DAVe3283/MIDI-Chimes/Firmware/Teensy3.1/Master/bsod_win10.cpp

#include "bsod_win10.h"
#include <stdint.h>

// const uint16_t bsod_bg_windows_xp(0x0010); // #000082 --> RGB565
// const uint16_t bsod_fg_windows_xp(0xFFFF); // #FFFFFF --> RGB565
const uint16_t bsod_bg_windows_10(0x2336); // #2067B2 --> RGB565
const uint16_t bsod_fg_windows_10(0xFFFF); // #FFFFFF --> RGB565

// Run-length encoded. Byte 0 is run length, 1-2 are color (little-endian).
const size_t bsod_frown_width(44);
const size_t bsod_frown_height(84); // Encoded height is only 42, but we mirror it
const uint8_t bsod_frown[] =
{
    0x24, 0x36, 0x23, 0x01, 0x56, 0x23, 0x06, 0x78, 0x54, 0x01, 0x38, 0x4C,
    0x24, 0x36, 0x23, 0x01, 0x1C, 0xA6, 0x06, 0xFF, 0xFF, 0x01, 0xD9, 0x6C,
    0x23, 0x36, 0x23, 0x01, 0x1A, 0x75, 0x06, 0xFF, 0xFF, 0x01, 0x1B, 0xA6,
    0x23, 0x36, 0x23, 0x01, 0x38, 0x4C, 0x01, 0xDF, 0xFF, 0x05, 0xFF, 0xFF,
    0x01, 0x1E, 0xD7, 0x01, 0x56, 0x23, 0x22, 0x36, 0x23, 0x01, 0x97, 0x33,
    0x01, 0x7E, 0xE7, 0x05, 0xFF, 0xFF, 0x01, 0xBF, 0xF7, 0x01, 0xF7, 0x3B,
    0x23, 0x36, 0x23, 0x01, 0x9D, 0xBE, 0x06, 0xFF, 0xFF, 0x01, 0x19, 0x75,
    0x23, 0x36, 0x23, 0x01, 0xD9, 0x6C, 0x06, 0xFF, 0xFF, 0x01, 0x9D, 0xBE,
    0x23, 0x36, 0x23, 0x01, 0x96, 0x2B, 0x01, 0x7E, 0xE7, 0x05, 0xFF, 0xFF,
    0x01, 0xBF, 0xF7, 0x01, 0xD7, 0x3B, 0x23, 0x36, 0x23, 0x01, 0xFB, 0xA5,
    0x06, 0xFF, 0xFF, 0x01, 0x5A, 0x85, 0x23, 0x36, 0x23, 0x01, 0x58, 0x54,
    0x06, 0xFF, 0xFF, 0x01, 0xFD, 0xCE, 0x01, 0x56, 0x23, 0x23, 0x36, 0x23,
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
    0x01, 0x9E, 0xEF, 0x02, 0x36, 0x23, 0x01, 0x56, 0x23, 0x01, 0x5E, 0xDF,
    0x01, 0x3E, 0xDF, 0x01, 0xF7, 0x3B, 0x3C, 0x36, 0x23, 0x02, 0xDD, 0xC6,
    0x3F, 0x36, 0x23, 0x02, 0xDD, 0xC6, 0x09, 0x36, 0x23, 0x01, 0x5E, 0xE7,
    0x01, 0x3C, 0xAE, 0x1B, 0x36, 0x23, 0x01, 0x96, 0x2B, 0x01, 0xBF, 0xF7,
    0x01, 0x7C, 0xBE, 0x02, 0x36, 0x23, 0x01, 0x38, 0x4C, 0x01, 0xFF, 0xFF,
    0x01, 0x19, 0x75, 0x04, 0x36, 0x23, 0x01, 0x56, 0x23, 0x01, 0x98, 0x5C,
    0x02, 0x3A, 0x7D, 0x01, 0x58, 0x54, 0x04, 0x36, 0x23, 0x01, 0xF7, 0x3B,
    0x01, 0x19, 0x75, 0x04, 0x36, 0x23, 0x01, 0x76, 0x2B, 0x01, 0x19, 0x75,
    0x01, 0xF7, 0x3B, 0x02, 0x36, 0x23, 0x01, 0x58, 0x54, 0x01, 0xD9, 0x6C,
    0x01, 0x36, 0x23, 0x01, 0xF7, 0x3B, 0x01, 0x19, 0x75, 0x01, 0xB7, 0x33,
    0x06, 0x36, 0x23, 0x01, 0x5E, 0xE7, 0x01, 0x3C, 0xAE, 0x04, 0x36, 0x23,
    0x01, 0xBB, 0x95, 0x01, 0xFF, 0xFF, 0x01, 0xB7, 0x33, 0x01, 0x36, 0x23,
    0x01, 0xBB, 0x95, 0x01, 0xFF, 0xFF, 0x01, 0x58, 0x54, 0x0E, 0x36, 0x23,
    0x01, 0x19, 0x75, 0x01, 0x18, 0x4C, 0x01, 0x36, 0x23, 0x01, 0x58, 0x54,
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
};

void draw_BSOD(ILI9341_t3& display)
{
    // Set colors
    display.fillScreen(bsod_bg_windows_10);
    display.setTextColor(bsod_fg_windows_10);

    // Decompression buffer (holds one row)
    uint16_t buffer[max(bsod_frown_width, bsod_text_width)];

    // Decompress :( emoticon
    size_t x(0);
    int16_t y(0);
    for (size_t i(0); i < (sizeof(bsod_frown) / sizeof(bsod_frown[0])); i += 3)
    {
        size_t run_length(bsod_frown[i]);
        const uint16_t color(*reinterpret_cast<const uint16_t*>(bsod_frown + i + 1));
        for (size_t run(0); run < run_length; ++run)
        {
            buffer[x++] = color;
            if (x >= bsod_frown_width)
            {
                // Draw the buffer
                display.writeRect(20, 20 + y++, bsod_frown_width, 1, buffer);
                display.writeRect(20, 20 + bsod_frown_height - y, bsod_frown_width, 1, buffer);
                x = 0; // Reset for next row
            }
        }
    }

    // Decompress useless generic Windows 10 BSOD text
    x = 0;
    y = 0;
    for (size_t i(0); i < (sizeof(bsod_text) / sizeof(bsod_text[0])); i += 3)
    {
        size_t run_length(bsod_text[i]);
        const uint16_t color(*reinterpret_cast<const uint16_t*>(bsod_text + i + 1));
        for (size_t run(0); run < run_length; ++run)
        {
            buffer[x++] = color;
            if (x >= bsod_text_width)
            {
                // Draw the buffer
                display.writeRect(78, 30 + y++, bsod_text_width, 1, buffer);
                x = 0; // Reset for next row
            }
        }
    }

    // Prepare to print error text
    display.setCursor(0, 124);
    display.setFontAdafruit();
}

void halt_system()
{
    while (true)
    {
        yield();
    }
}
